yas-sim/floppy_disk_shield_2d/resources/fd-shield3a.jpg

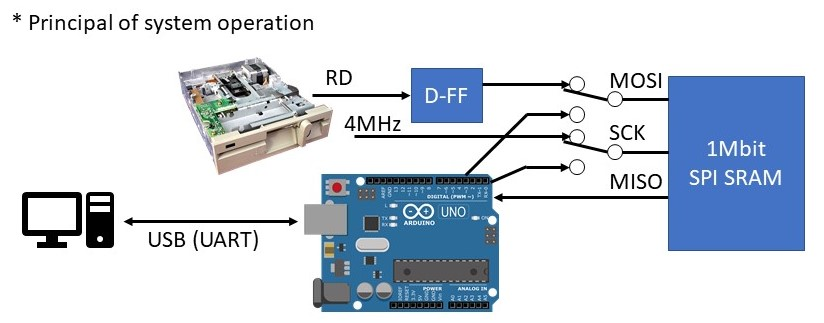
resources/fd-shield3a.jpg
