yas-sim/floppy_disk_shield_2d/resources/fd-shield.jpg

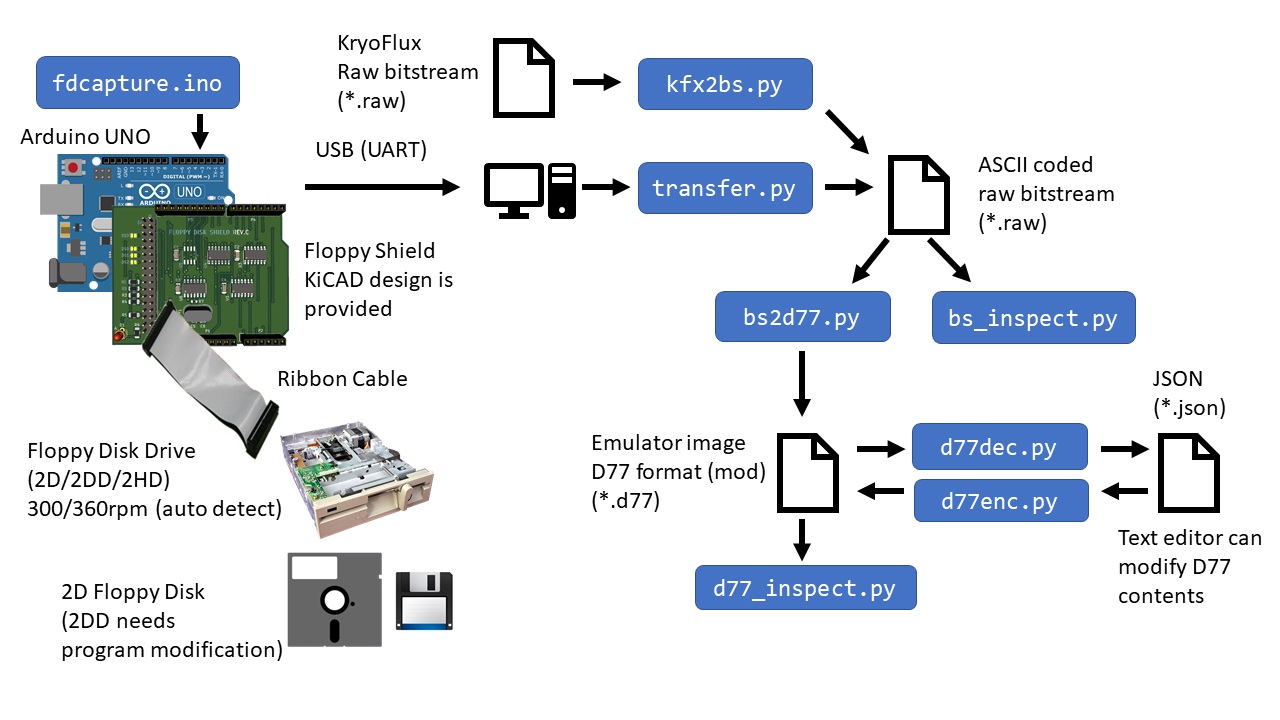
resources/fd-shield.jpg
